OperatorDishS0ap/DS-Airsoft-Grenade/V5/Images/cam_asm.JPEG

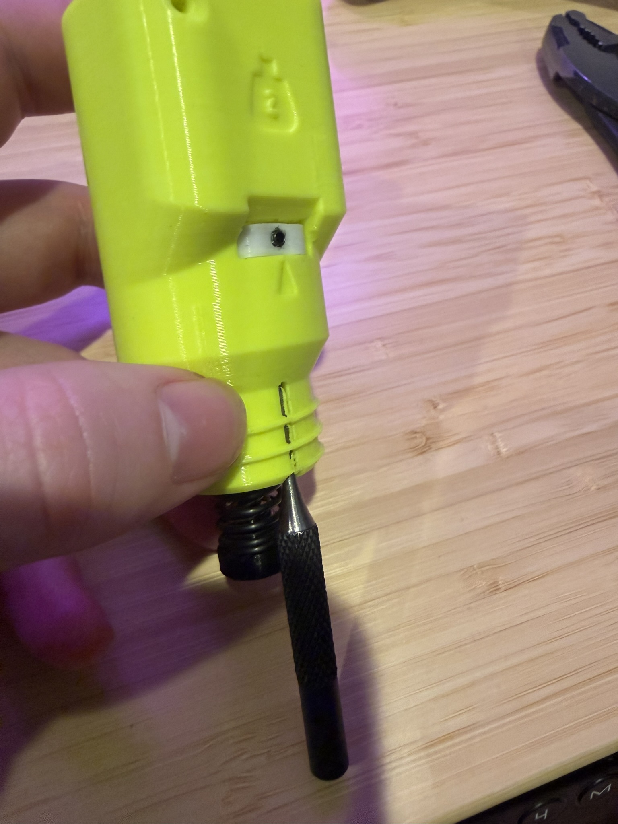
V5/Images/cam_asm.JPEG
