OperatorDishS0ap/DS-Airsoft-Grenade/Depricated/V4/8CapBodies/Retainer.STEP

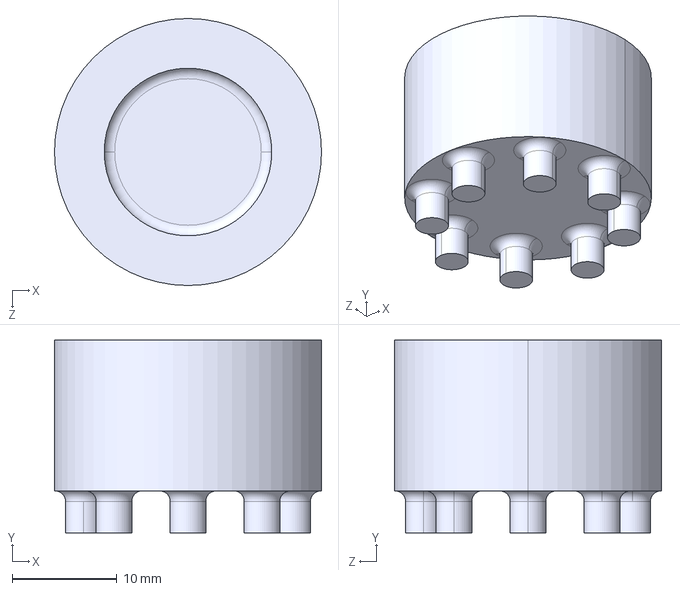
[picture p55: CAD file, 2025-09-30]
Depricated/V4/8CapBodies/Retainer.STEP
25.5 x 18.4 x 25.5 mm
