OperatorDishS0ap/DS-Airsoft-Grenade/Depricated/V4/ImpactFuse/Spoons/Spoon61P.STEP

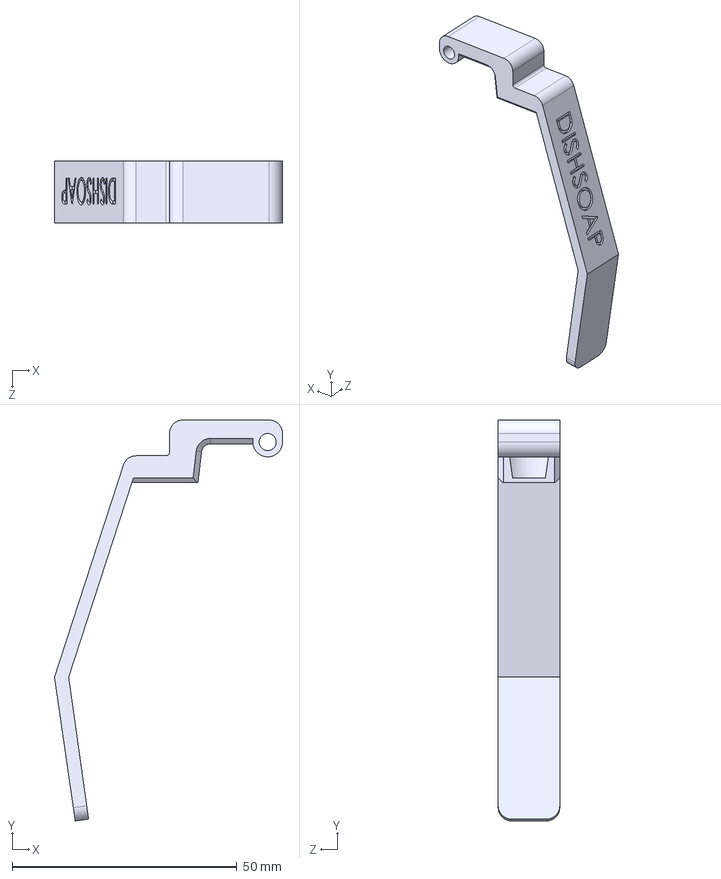
[picture p56: CAD file, 2025-09-30]
Depricated/V4/ImpactFuse/Spoons/Spoon61P.STEP
50.7 x 89.2 x 13.7 mm
