OperatorDishS0ap/DS-Airsoft-Grenade/Depricated/V4/PrimerBodies/DS38PL.STEP

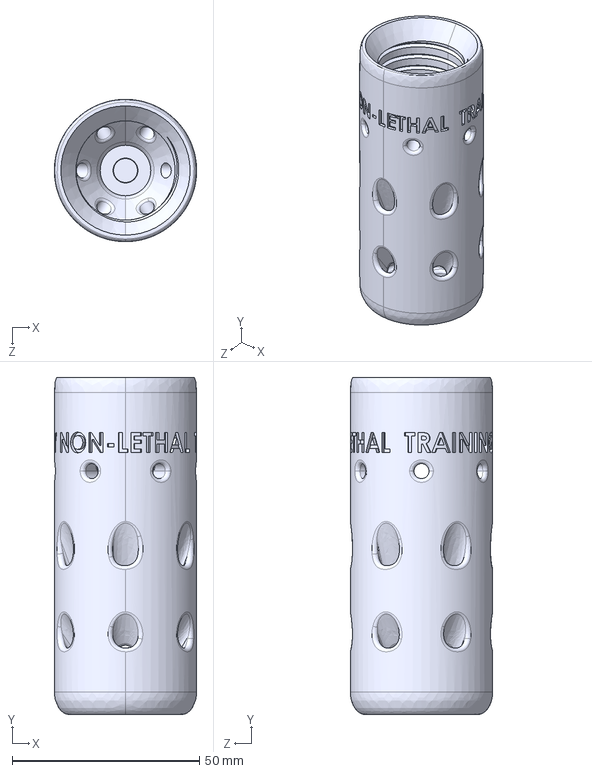
[picture p57: CAD file, 2026-01-04]
Depricated/V4/PrimerBodies/DS38PL.STEP
38.0 x 90.0 x 38.0 mm
