OperatorDishS0ap/DS-Airsoft-Grenade/Depricated/V4/SnapBodies/DS38STop.STEP

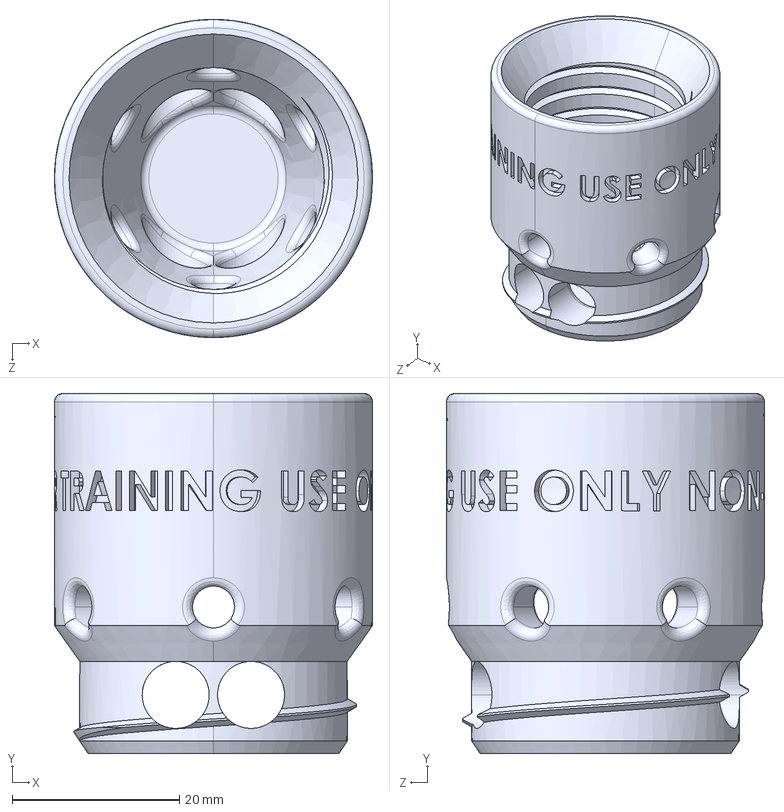
[picture p58: CAD file, 2026-01-04]
Depricated/V4/SnapBodies/DS38STop.STEP
38.0 x 43.0 x 38.0 mm
