OperatorDishS0ap/DS-Airsoft-Grenade/Depricated/V4/TimedFuse/BasicTimer/TimerCapRecharge.STEP

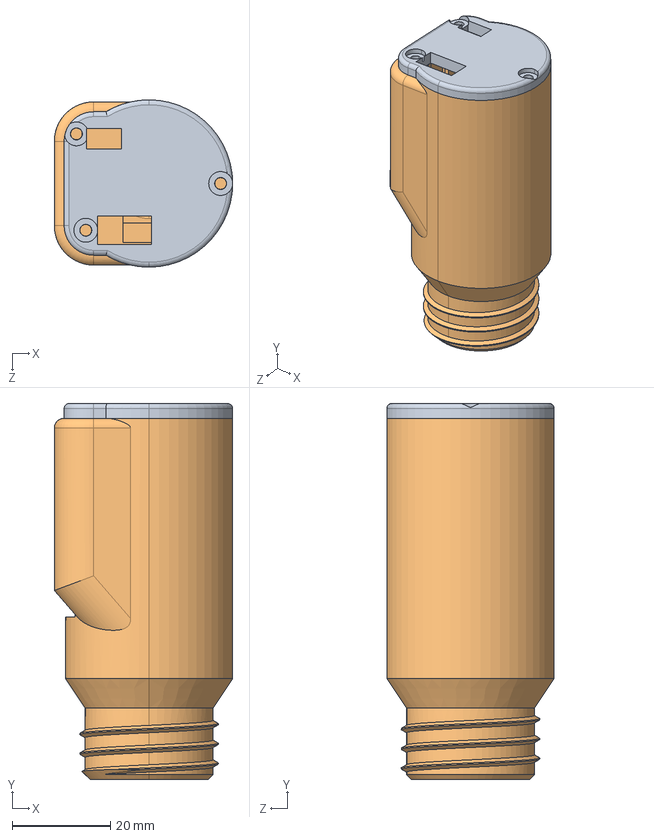
[picture p59: CAD file, 2025-09-30]
Depricated/V4/TimedFuse/BasicTimer/TimerCapRecharge.STEP
36.3 x 76.4 x 34.0 mm
