OperatorDishS0ap/DS-Airsoft-Grenade/Depricated/V4/TimedFuse/PCBTimer/timerV4pcb.STEP

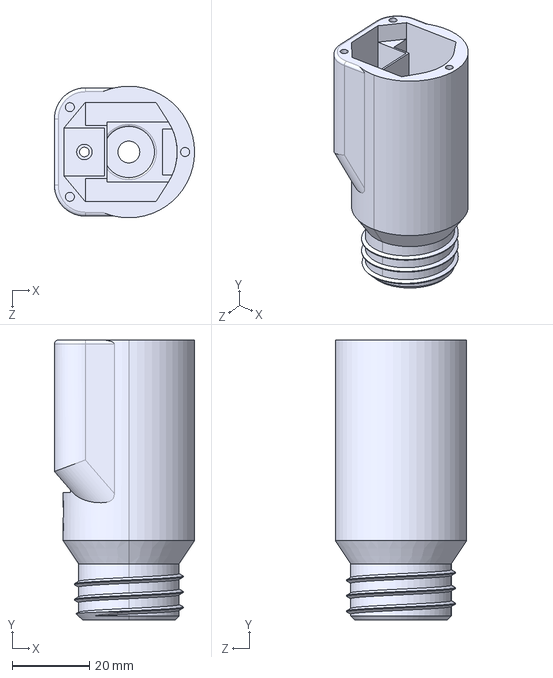
[picture p60: CAD file, 2025-09-30]
Depricated/V4/TimedFuse/PCBTimer/timerV4pcb.STEP
36.3 x 72.4 x 34.0 mm
