OperatorDishS0ap/DS-Airsoft-Grenade/V5/STL/ImpactFuse/Spoon/Spoon38PrimerLongV5.STL

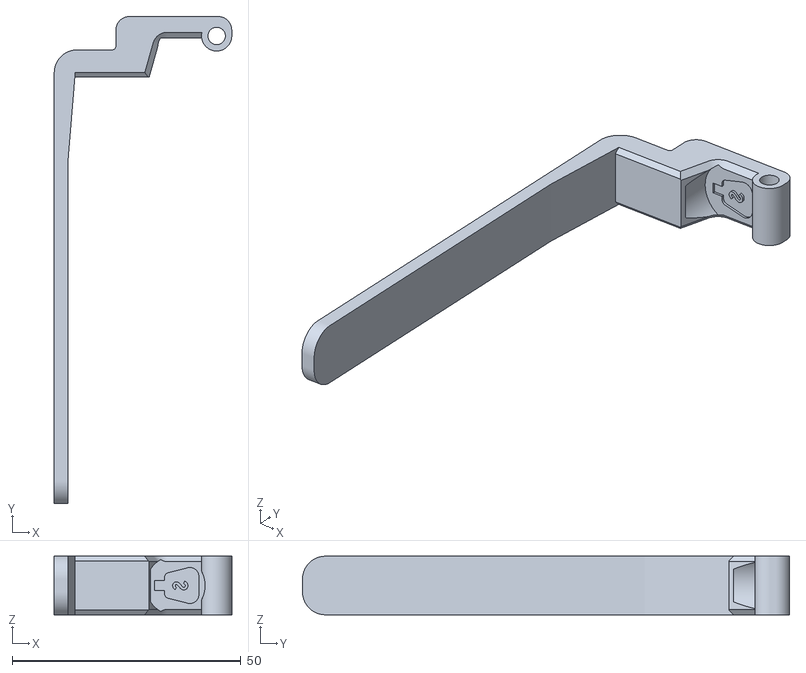
[picture p61: CAD file, 2026-03-10]
V5/STL/ImpactFuse/Spoon/Spoon38PrimerLongV5.STL
38.8 x 106.4 x 12.8
