OperatorDishS0ap/DS-Airsoft-Grenade/V5/STL/PrimerBody/TestHole.STL

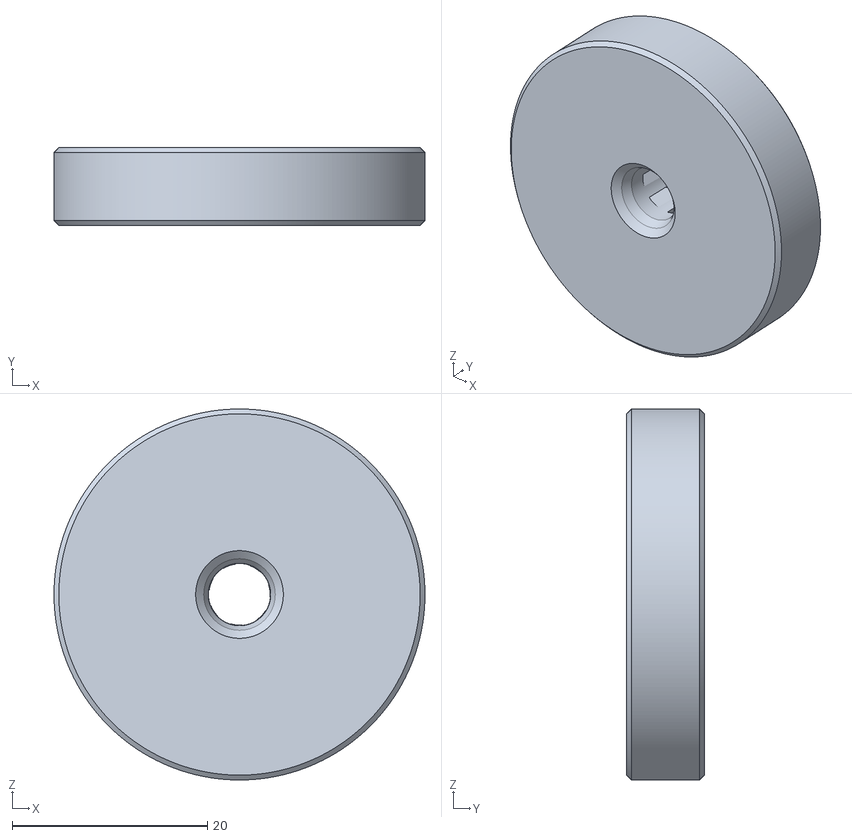
[picture p62: CAD file, 2026-03-10]
V5/STL/PrimerBody/TestHole.STL
38.0 x 8.00 x 38.0
