OperatorDishS0ap/DS-Airsoft-Grenade/V5/STL/SnapBody/DS55V5Base.STL

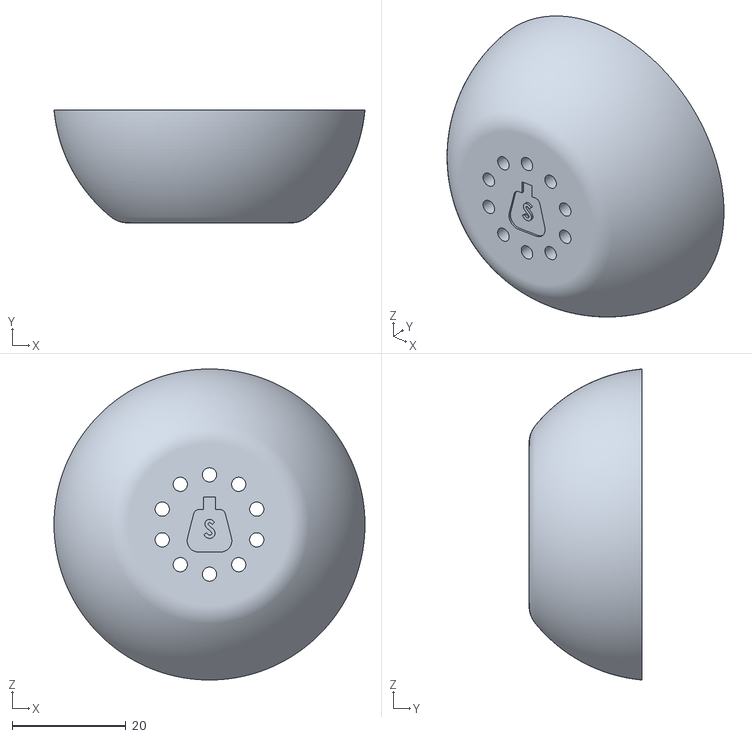
[picture p63: CAD file, 2026-03-10]
V5/STL/SnapBody/DS55V5Base.STL
54.8 x 19.9 x 54.8
