OperatorDishS0ap/DS-Airsoft-Grenade/V5/STL/TimedFuse/CapV5.STL

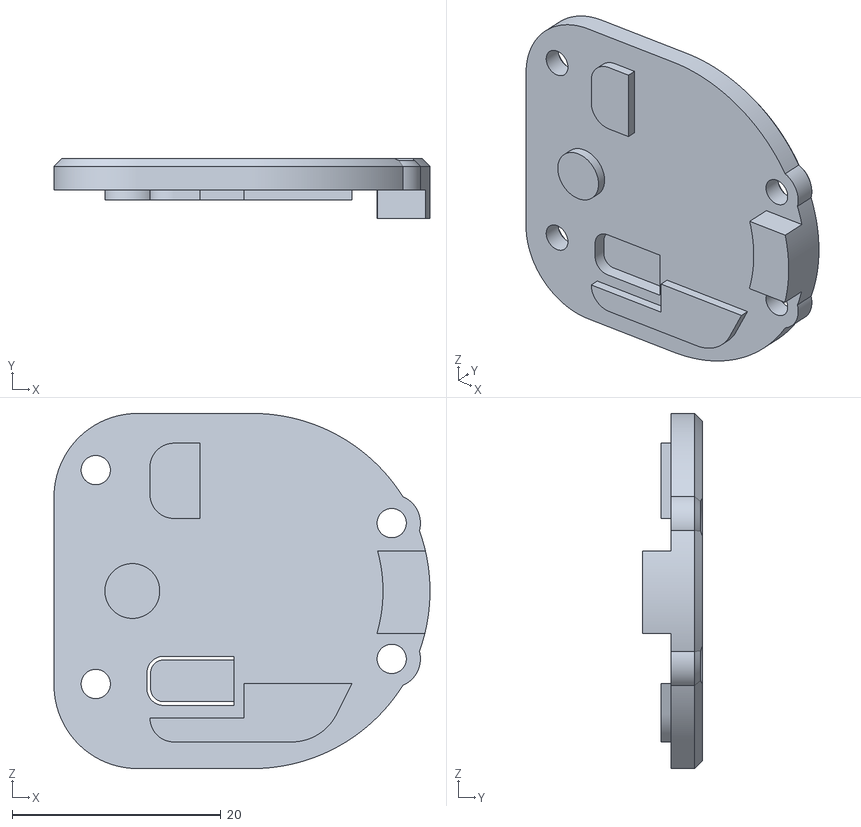
[picture p64: CAD file, 2026-03-10]
V5/STL/TimedFuse/CapV5.STL
36.0 x 5.75 x 34.0
