OperatorDishS0ap/DS-Airsoft-Grenade/Depricated/V4/8CapBodies/DS388.STEP

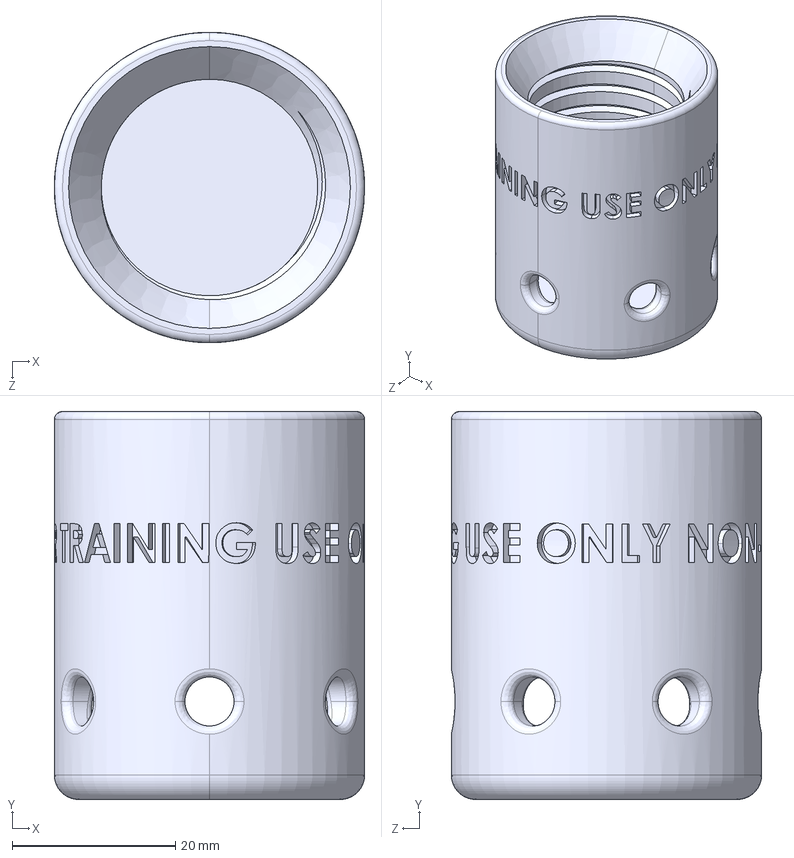
[picture p65: CAD file, 2025-09-30]
Depricated/V4/8CapBodies/DS388.STEP
38.0 x 47.5 x 38.0 mm
