OperatorDishS0ap/DS-Airsoft-Grenade/Depricated/V4/ImpactFuse/Spoons/Spoon38P.STEP

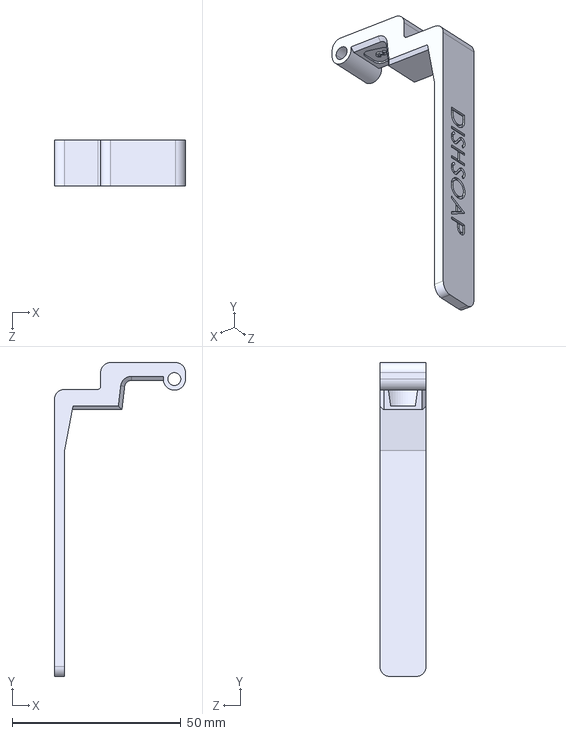
[picture p66: CAD file, 2025-09-30]
Depricated/V4/ImpactFuse/Spoons/Spoon38P.STEP
38.8 x 93.0 x 13.7 mm
