OperatorDishS0ap/DS-Airsoft-Grenade/Depricated/V4/PrimerBodies/DS61P.STEP

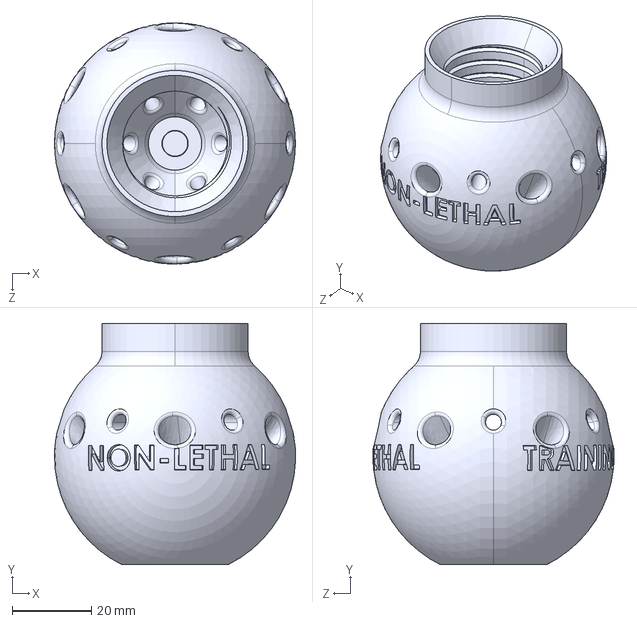
[picture p67: CAD file, 2026-01-04]
Depricated/V4/PrimerBodies/DS61P.STEP
61.0 x 61.0 x 61.0 mm
