OperatorDishS0ap/DS-Airsoft-Grenade/Depricated/V4/SnapBodies/DS55SBottom.STEP

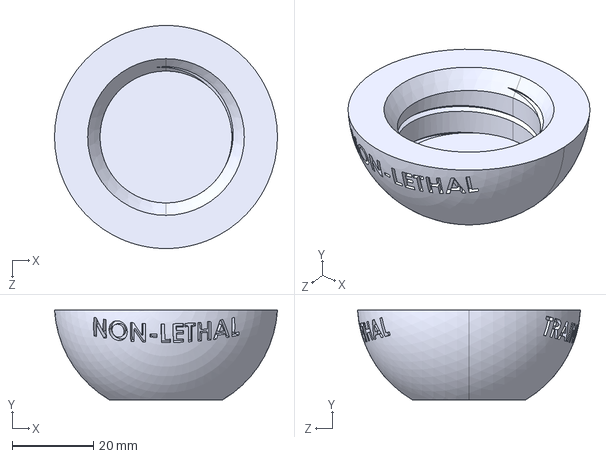
[picture p68: CAD file, 2025-09-30]
Depricated/V4/SnapBodies/DS55SBottom.STEP
54.9 x 22.1 x 54.9 mm
