OperatorDishS0ap/DS-Airsoft-Grenade/Depricated/V4/TimedFuse/BasicTimer/TimerCap2032.STEP

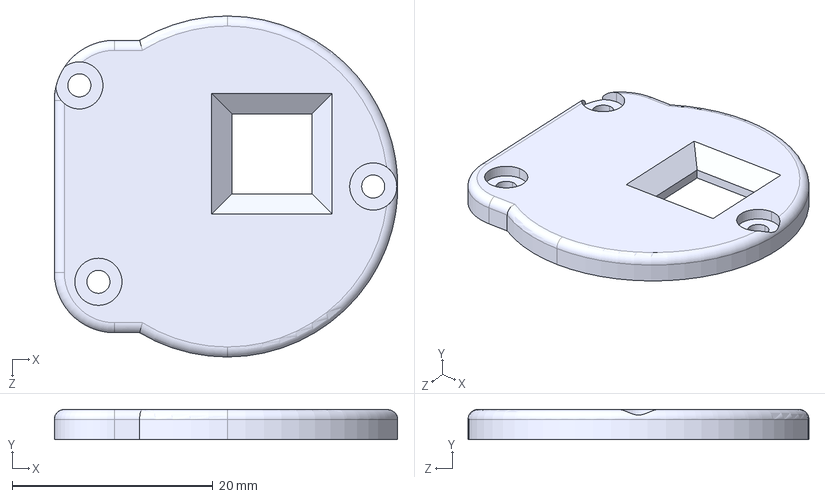
[picture p69: CAD file, 2025-09-30]
Depricated/V4/TimedFuse/BasicTimer/TimerCap2032.STEP
34.2 x 3.00 x 34.0 mm
