OperatorDishS0ap/DS-Airsoft-Grenade/Depricated/V4/TimedFuse/SpringPlate_NylonNut.STEP

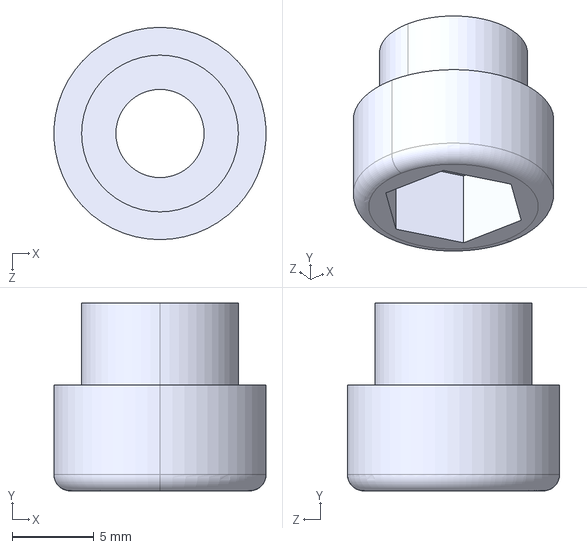
[picture p70: CAD file, 2025-09-30]
Depricated/V4/TimedFuse/SpringPlate_NylonNut.STEP
13.0 x 11.5 x 13.0 mm
