OperatorDishS0ap/DS-Airsoft-Grenade/V5/STL/ImpactFuse/Spoon/Spoon38PrimerV5.STL

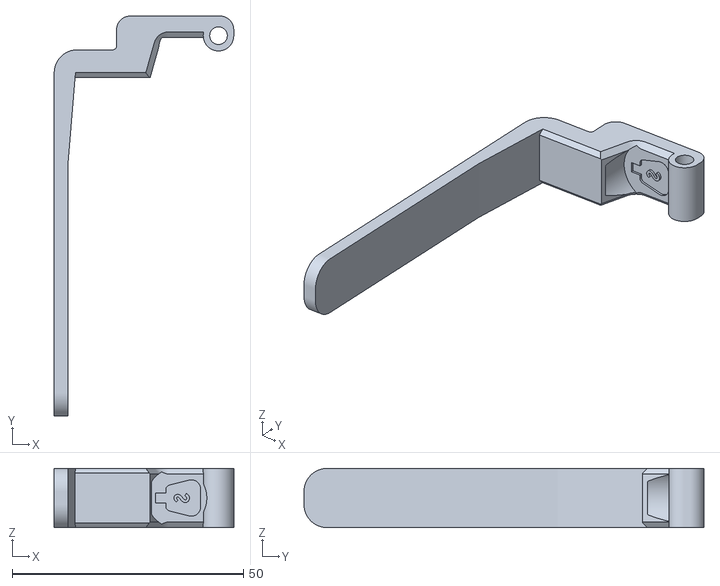
[picture p71: CAD file, 2026-03-10]
V5/STL/ImpactFuse/Spoon/Spoon38PrimerV5.STL
38.8 x 86.4 x 12.8
