OperatorDishS0ap/DS-Airsoft-Grenade/V5/STL/SnapBody/DS38V5Base.STL

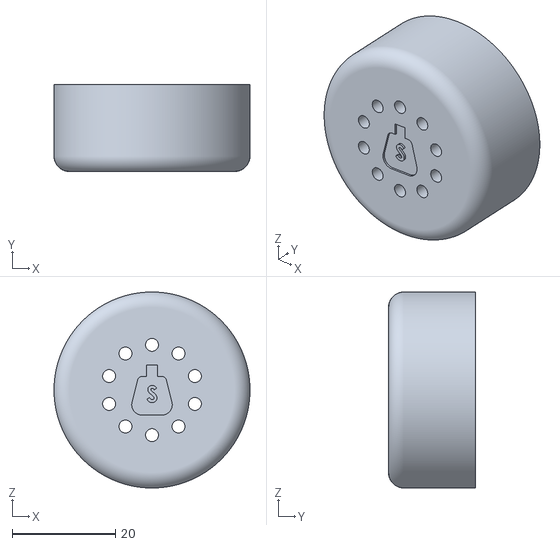
[picture p72: CAD file, 2026-03-10]
V5/STL/SnapBody/DS38V5Base.STL
38.0 x 16.9 x 38.0
