OperatorDishS0ap/DS-Airsoft-Grenade/V5/STL/TimedFuse/SwitchLeverV5.STL

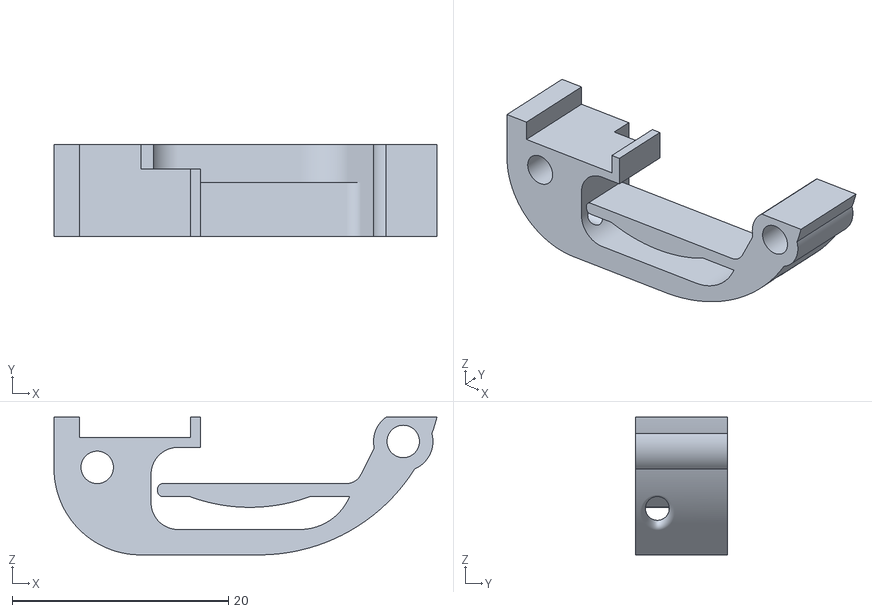
[picture p73: CAD file, 2026-03-10]
V5/STL/TimedFuse/SwitchLeverV5.STL
35.5 x 8.50 x 12.8
