OperatorDishS0ap/DS-Airsoft-Grenade/Depricated/V4/8CapBodies/DS388F.STEP

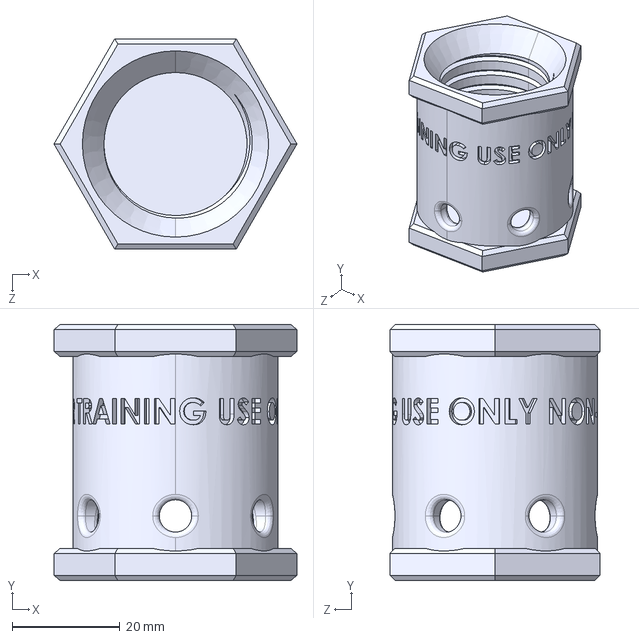
[picture p74: CAD file, 2025-09-30]
Depricated/V4/8CapBodies/DS388F.STEP
45.0 x 47.5 x 39.0 mm
