OperatorDishS0ap/DS-Airsoft-Grenade/Depricated/V4/ImpactFuse/Spoons/SpoonThumb.STEP

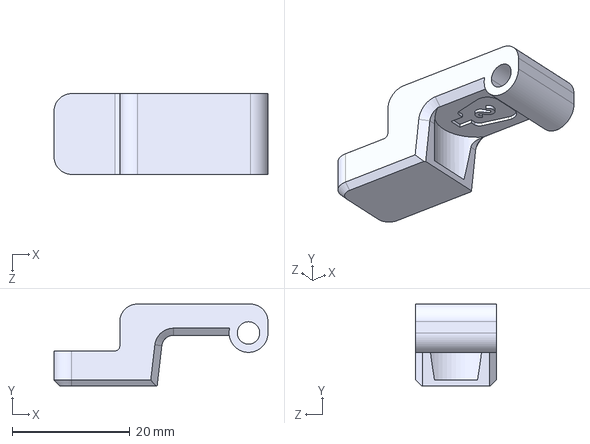
[picture p75: CAD file, 2025-09-30]
Depricated/V4/ImpactFuse/Spoons/SpoonThumb.STEP
36.3 x 13.9 x 13.7 mm
