OperatorDishS0ap/DS-Airsoft-Grenade/Depricated/V4/PrimerBodies/DS38P.STEP

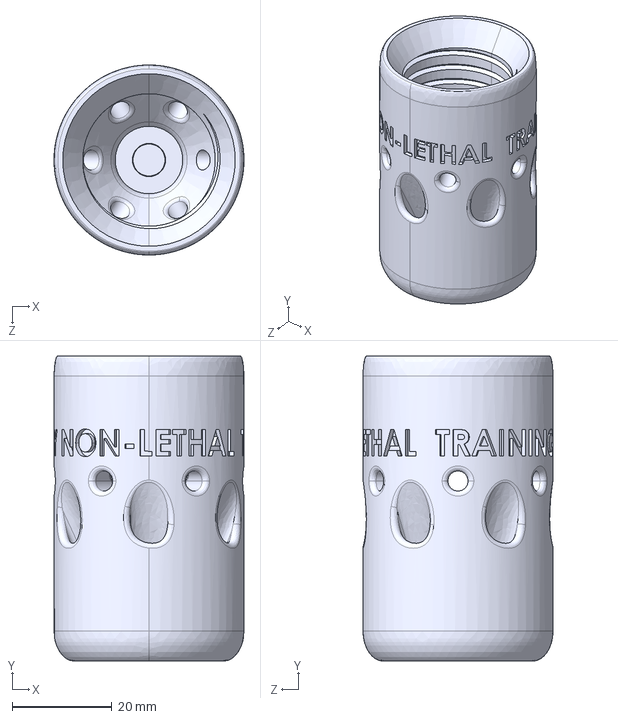
[picture p76: CAD file, 2026-01-04]
Depricated/V4/PrimerBodies/DS38P.STEP
38.0 x 61.0 x 38.0 mm
