OperatorDishS0ap/DS-Airsoft-Grenade/Depricated/V4/SnapBodies/DS38SFBottom.STEP

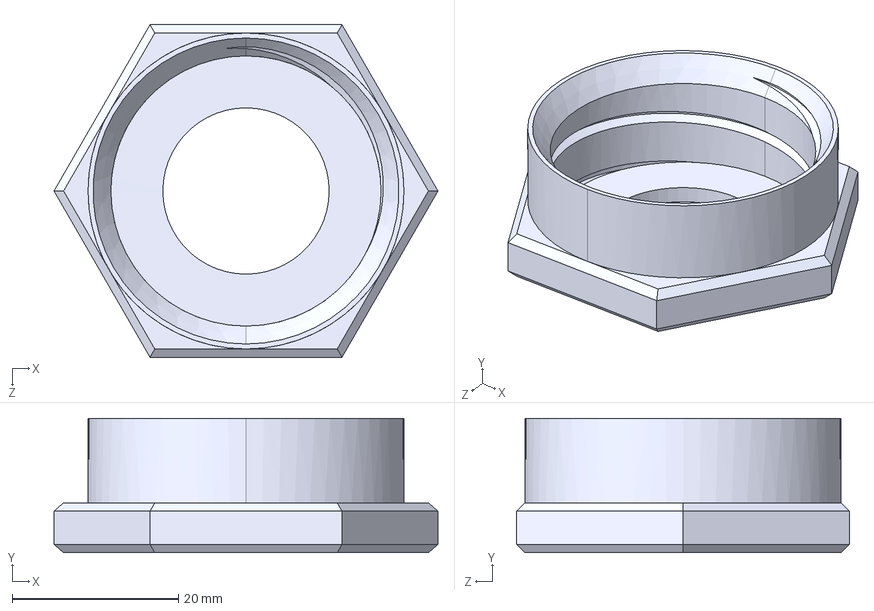
[picture p77: CAD file, 2025-09-30]
Depricated/V4/SnapBodies/DS38SFBottom.STEP
46.2 x 16.2 x 40.0 mm
