OperatorDishS0ap/DS-Airsoft-Grenade/Depricated/V4/TimedFuse/Cam.STEP

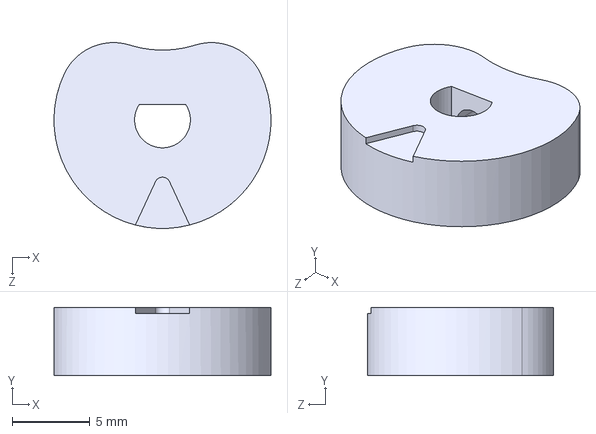
[picture p78: CAD file, 2025-09-30]
Depricated/V4/TimedFuse/Cam.STEP
14.0 x 4.40 x 12.0 mm
