OperatorDishS0ap/DS-Airsoft-Grenade/V5/STL/ImpactFuse/Spoon/Spoon38CapHexV5.STL

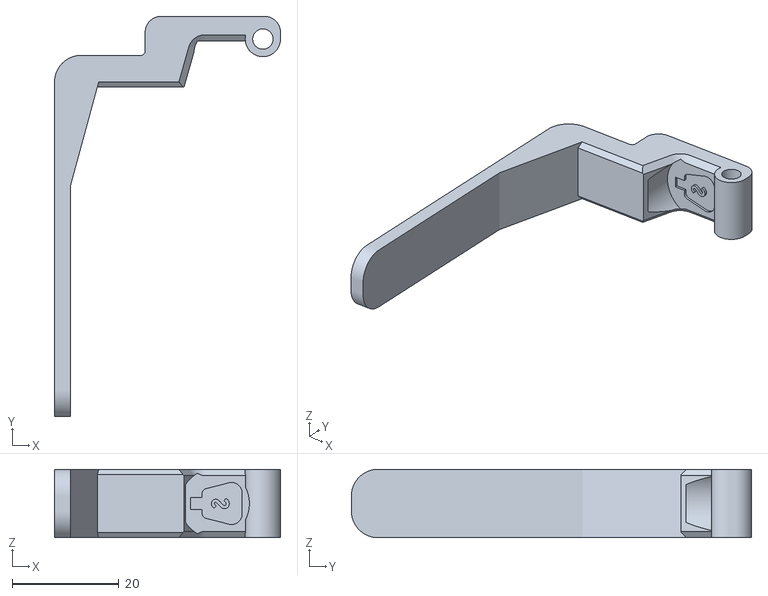
[picture p79: CAD file, 2026-03-10]
V5/STL/ImpactFuse/Spoon/Spoon38CapHexV5.STL
42.3 x 74.9 x 12.8
