OperatorDishS0ap/DS-Airsoft-Grenade/V5/STL/TimedFuse/SpringPlateV5.STL

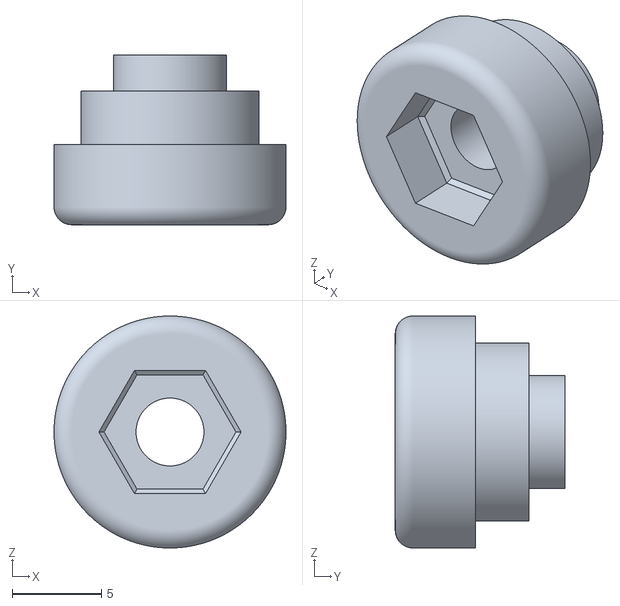
[picture p80: CAD file, 2026-03-10]
V5/STL/TimedFuse/SpringPlateV5.STL
13.0 x 9.50 x 13.0
