OperatorDishS0ap/DS-Airsoft-Grenade/Depricated/V4/ImpactFuse/Spoons/Spoon38PL.STEP

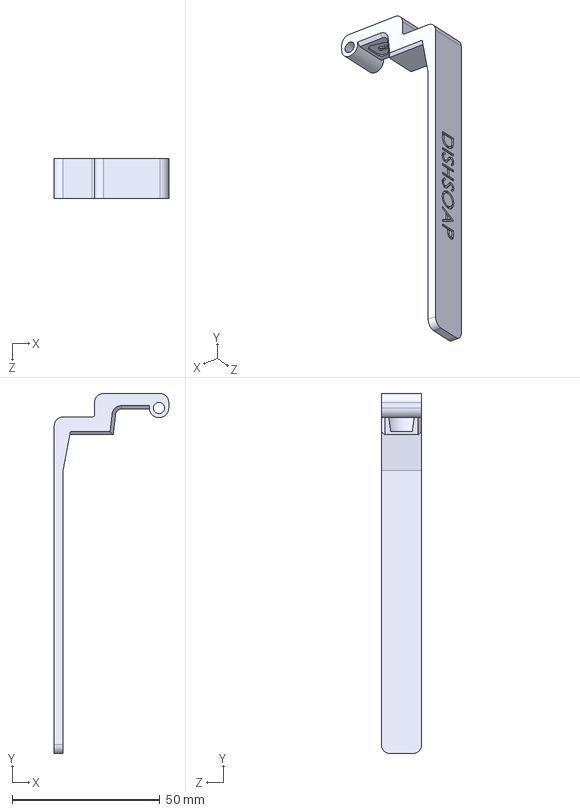
[picture p81: CAD file, 2025-09-30]
Depricated/V4/ImpactFuse/Spoons/Spoon38PL.STEP
38.8 x 122.0 x 13.7 mm
