OperatorDishS0ap/DS-Airsoft-Grenade/Depricated/V4/PrimerBodies/DS38PFL.STEP

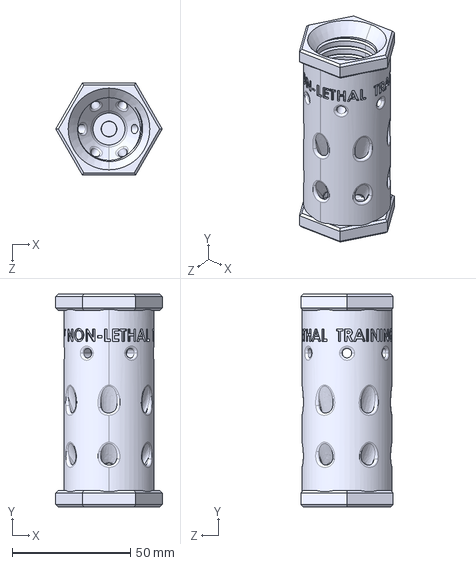
[picture p82: CAD file, 2026-01-04]
Depricated/V4/PrimerBodies/DS38PFL.STEP
45.0 x 90.0 x 39.0 mm
