OperatorDishS0ap/DS-Airsoft-Grenade/Depricated/V4/SnapBodies/DS38SBottom.STEP

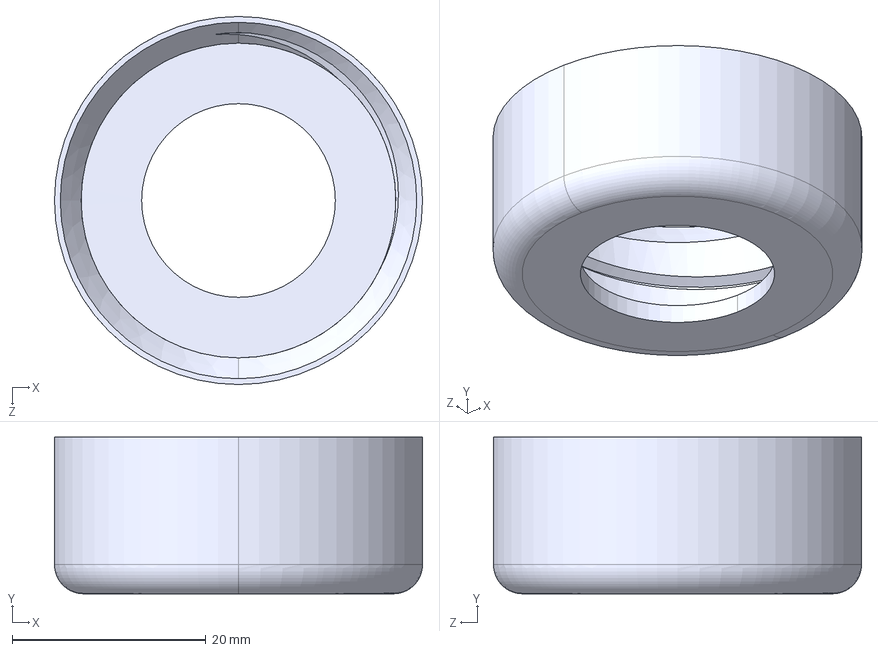
[picture p83: CAD file, 2025-09-30]
Depricated/V4/SnapBodies/DS38SBottom.STEP
38.0 x 16.2 x 38.0 mm
