OperatorDishS0ap/DS-Airsoft-Grenade/V5/STL/ImpactFuse/Spoon/Spoon55SnapV5.STL

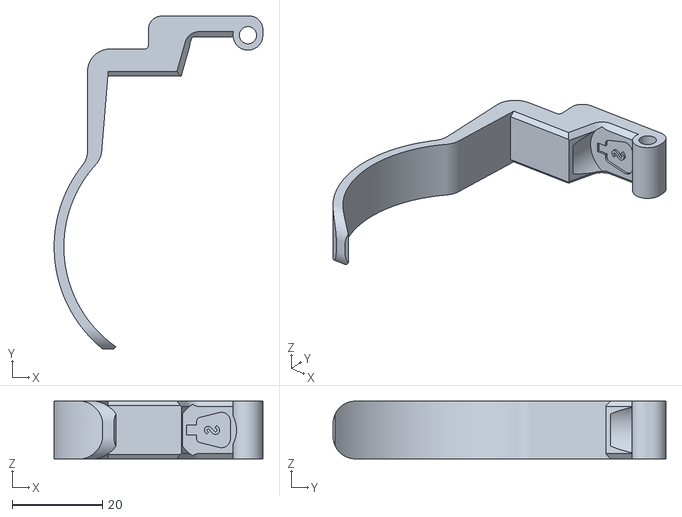
[picture p84: CAD file, 2026-03-10]
V5/STL/ImpactFuse/Spoon/Spoon55SnapV5.STL
46.2 x 73.7 x 12.8
