OperatorDishS0ap/DS-Airsoft-Grenade/V5/STL/TimedFuse/PCBPinFuseV5.STL

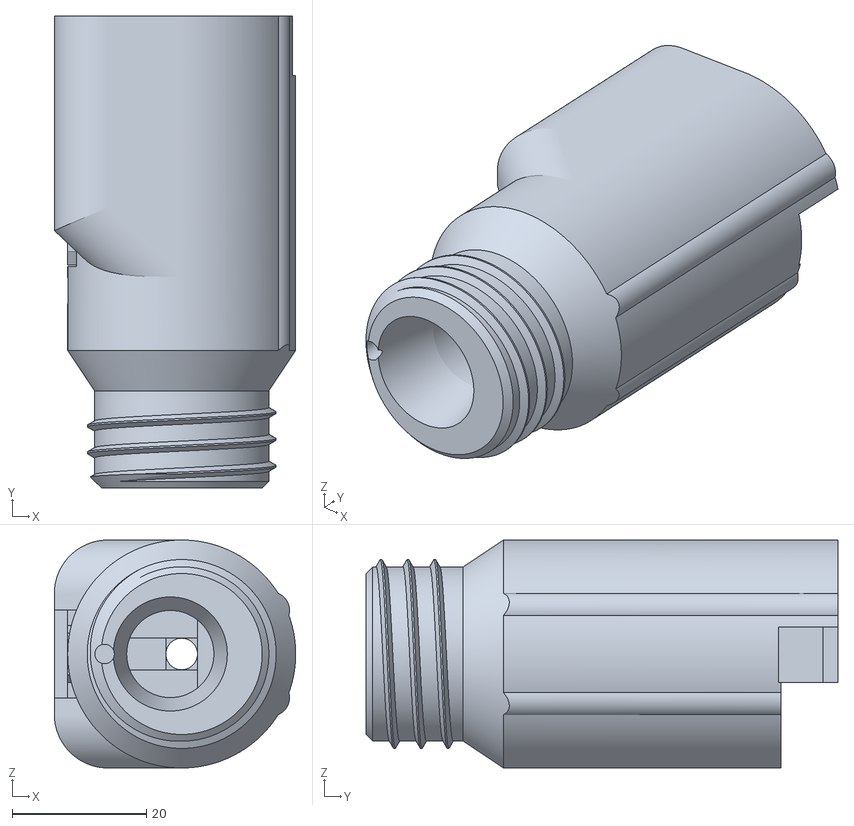
[picture p85: CAD file, 2026-03-10]
V5/STL/TimedFuse/PCBPinFuseV5.STL
36.0 x 70.4 x 34.0
