OperatorDishS0ap/DS-Airsoft-Grenade/Depricated/V4/ImpactFuse/Spoons/Spoon55S_8.STEP

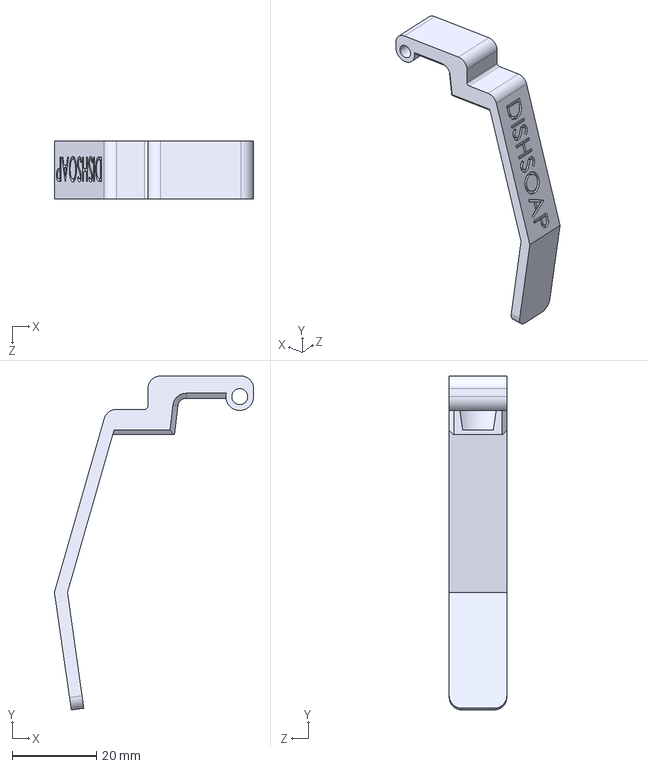
[picture p86: CAD file, 2025-09-30]
Depricated/V4/ImpactFuse/Spoons/Spoon55S_8.STEP
47.4 x 79.5 x 13.7 mm
