OperatorDishS0ap/DS-Airsoft-Grenade/Depricated/V4/SnapBodies/DS55STop.STEP

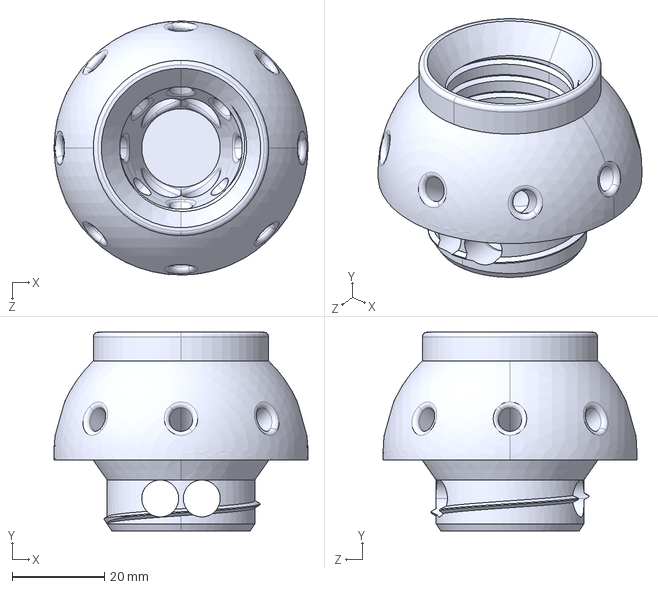
[picture p87: CAD file, 2025-09-30]
Depricated/V4/SnapBodies/DS55STop.STEP
55.0 x 43.0 x 55.0 mm
