OperatorDishS0ap/DS-Airsoft-Grenade/V5/STL/ImpactFuse/Spoon/Spoon38PrimerHexV5.STL

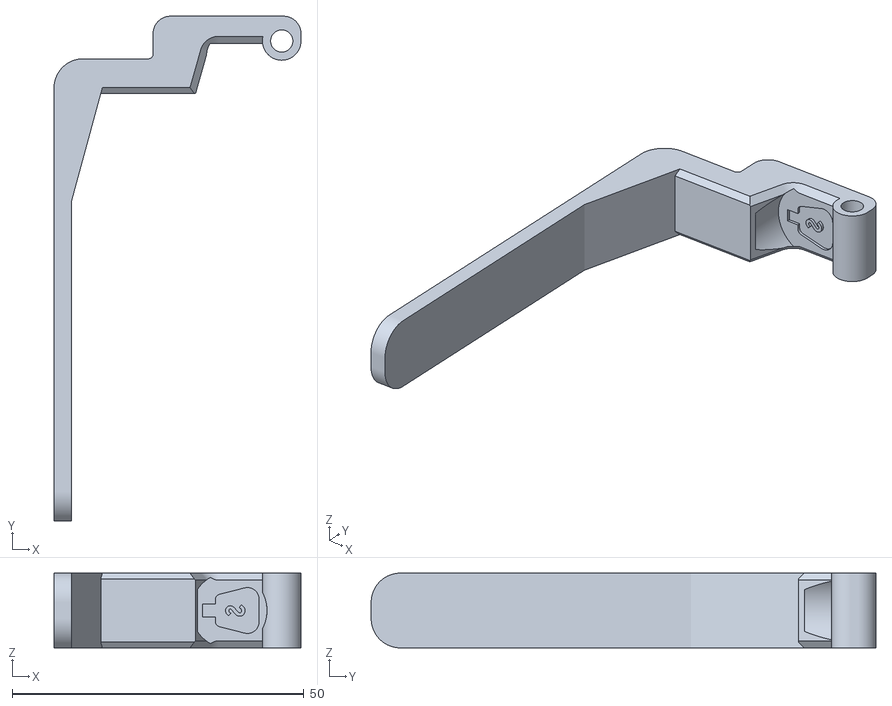
[picture p88: CAD file, 2026-03-10]
V5/STL/ImpactFuse/Spoon/Spoon38PrimerHexV5.STL
42.3 x 86.4 x 12.8
