OperatorDishS0ap/DS-Airsoft-Grenade/V5/STL/ImpactFuse/Spoon/Spoon38CapV5.STL

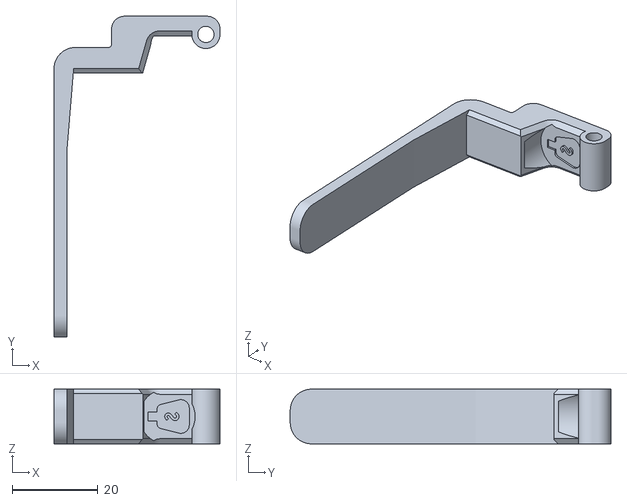
[picture p89: CAD file, 2026-03-10]
V5/STL/ImpactFuse/Spoon/Spoon38CapV5.STL
38.8 x 74.9 x 12.8
