OperatorDishS0ap/DS-Airsoft-Grenade/V5/STL/ImpactFuse/Spoon/Spoon38SnapV5.STL

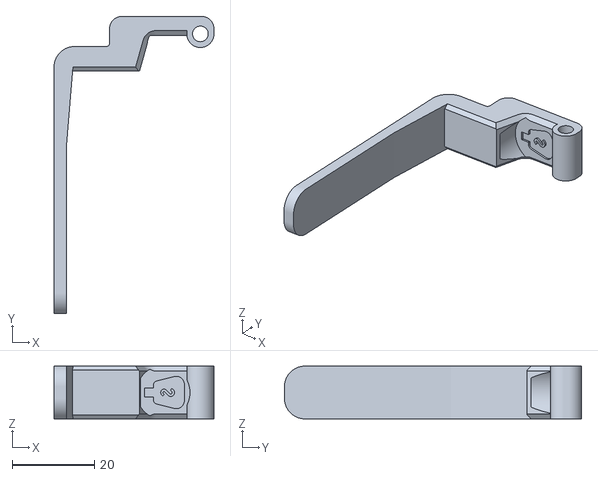
[picture p90: CAD file, 2026-03-10]
V5/STL/ImpactFuse/Spoon/Spoon38SnapV5.STL
38.8 x 72.1 x 12.8
