OperatorDishS0ap/DS-Airsoft-Grenade/V5/STL/ImpactFuse/Spoon/Spoon61PrimerV5.STL

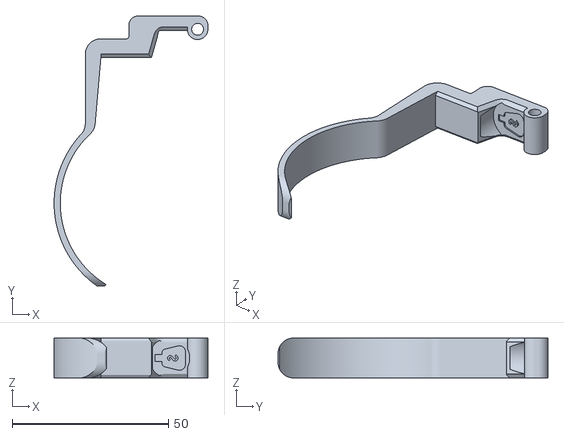
[picture p91: CAD file, 2026-03-10]
V5/STL/ImpactFuse/Spoon/Spoon61PrimerV5.STL
49.3 x 86.5 x 12.8
