OperatorDishS0ap/DS-Airsoft-Grenade/V5/STL/ImpactFuse/Spoon/Spoon38SnapHexV5.STL

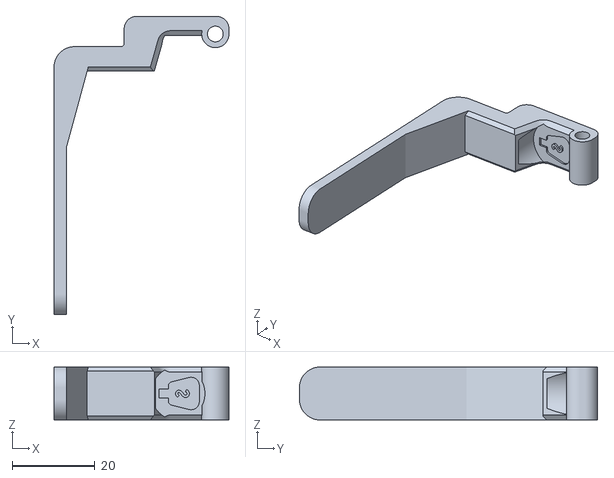
[picture p92: CAD file, 2026-03-10]
V5/STL/ImpactFuse/Spoon/Spoon38SnapHexV5.STL
42.3 x 72.1 x 12.8
