OperatorDishS0ap/DS-Airsoft-Grenade/V5/STL/ImpactFuse/Spoon/Spoon55CapV5.STL

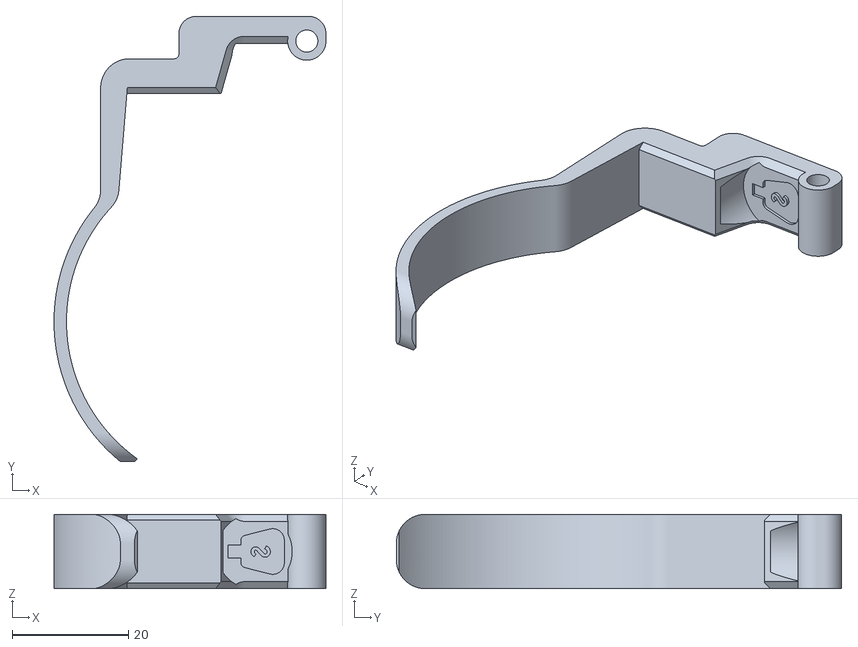
[picture p93: CAD file, 2026-03-10]
V5/STL/ImpactFuse/Spoon/Spoon55CapV5.STL
46.8 x 76.7 x 12.8
